HIGHVOLTAGEBEE/PowerMeterV2/images/1.jpg

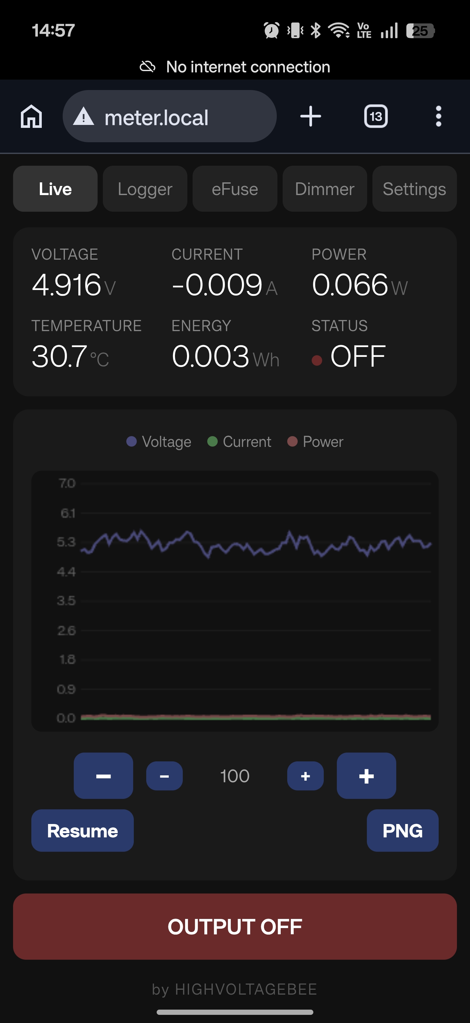
images/1.jpg
