HIGHVOLTAGEBEE/PowerMeterV2/images/2.jpg

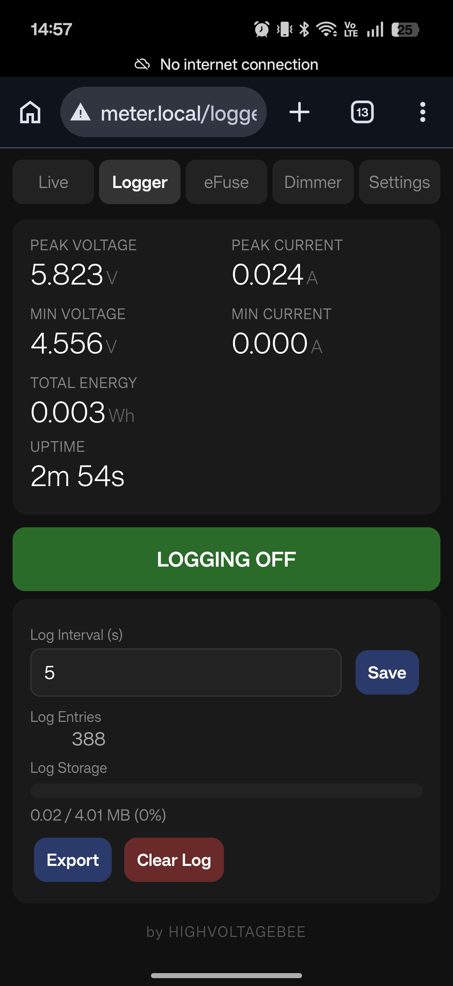
images/2.jpg
