HIGHVOLTAGEBEE/PowerMeterV2/images/3.jpg

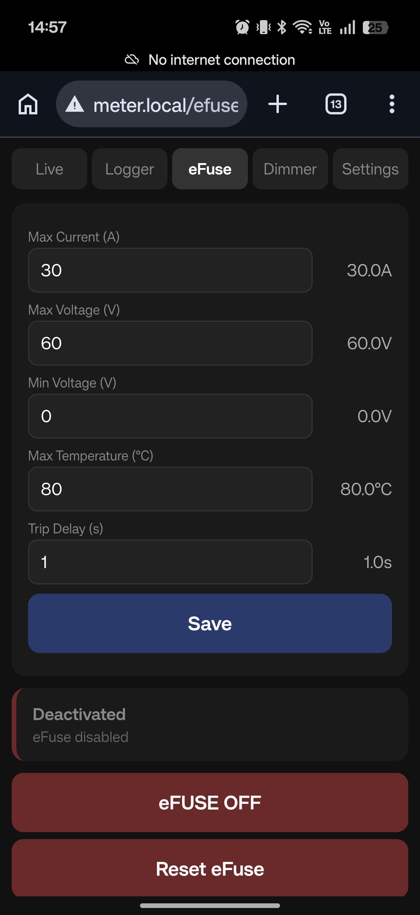
images/3.jpg
