HIGHVOLTAGEBEE/PowerMeterV2/images/4.jpg

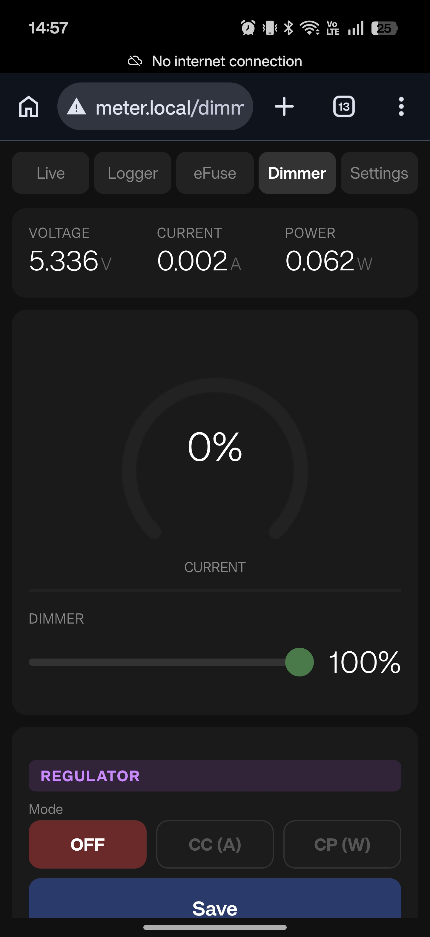
images/4.jpg
