HIGHVOLTAGEBEE/PowerMeterV2/images/5.jpg

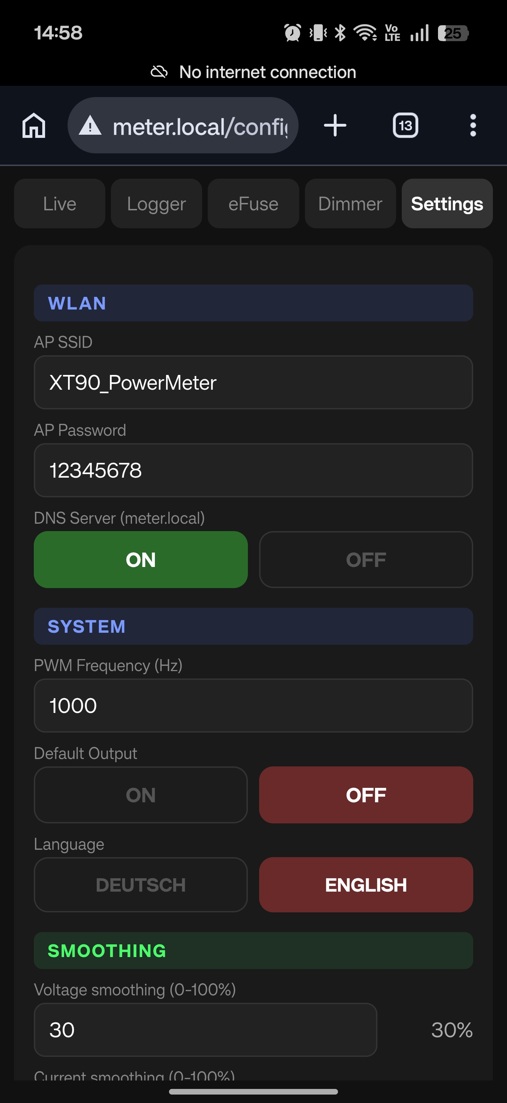
images/5.jpg
